MohamedKhay154/stm32-sim7600-gps-4g-lte-anti-theft-tracker/docs/scrennshots/PCB/Layout.png

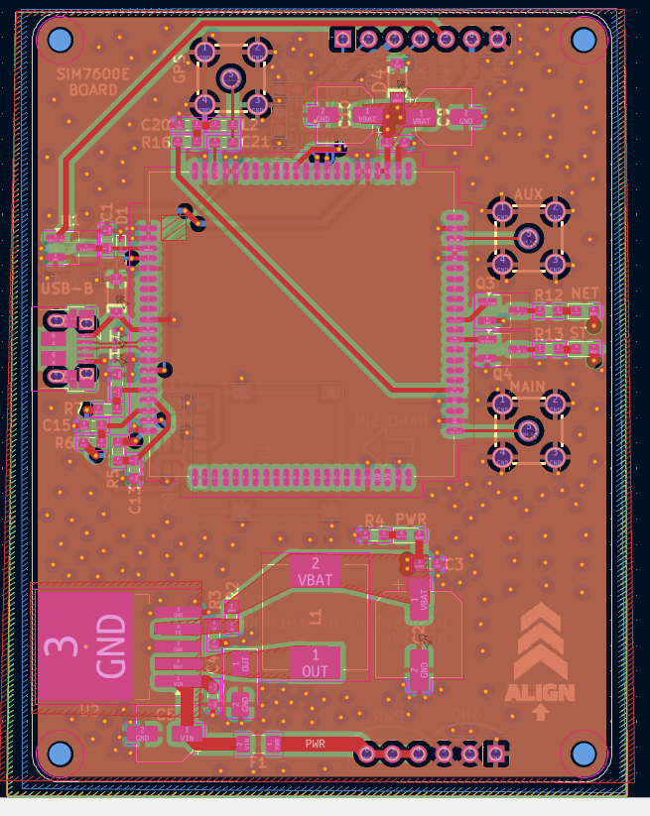
docs/scrennshots/PCB/Layout.png
