MohamedKhay154/stm32-sim7600-gps-4g-lte-anti-theft-tracker/firmware/SIM7600e.ioc

Mcu.UserName=STM32L476RGTx
PA2.GPIO_Label=USART_TX
PA2.Signal=USART2_TX
PA3.GPIO_Label=USART_RX
PA3.Signal=USART2_RX
PA5.GPIO_Label=LD2 [green Led]
PA5.Signal=GPIO_Output
PC13.GPIO_Label=B1 [Blue PushButton]
PC13.Signal=GPXTI13
PC4.Signal=USART3_TX
PC5.Signal=USART3_RX
PC6.Signal=GPXTI6
PC7.Signal=GPIO_Output
